v9938/MSX4SlotExpander/PCB/GarberFiles/Bottom.png

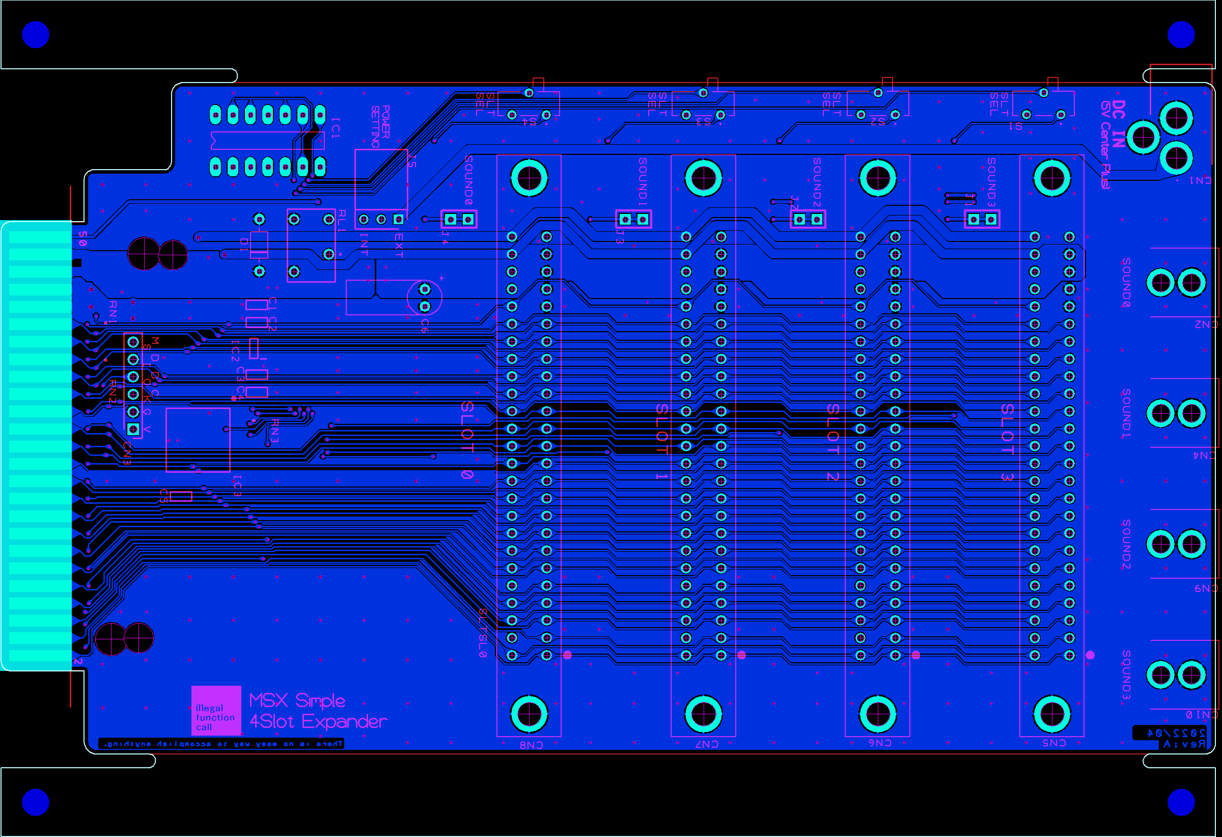
PCB/GarberFiles/Bottom.png
