v9938/MSX4SlotExpander/PCB/GarberFiles/top.png

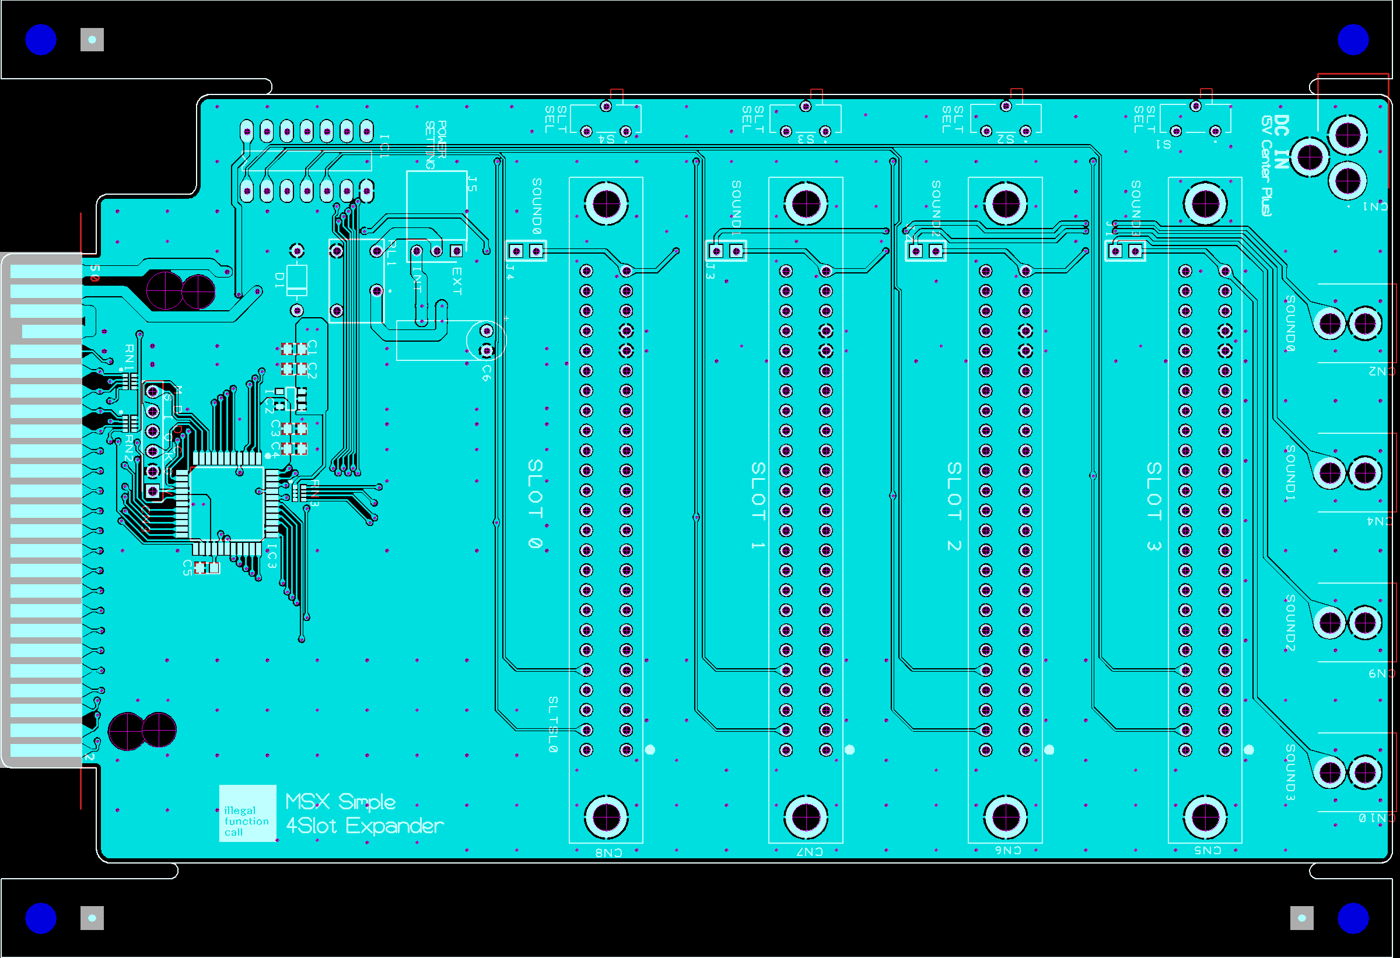
PCB/GarberFiles/top.png
